antmicro/polarfire-som/assets/previews/layer1.png

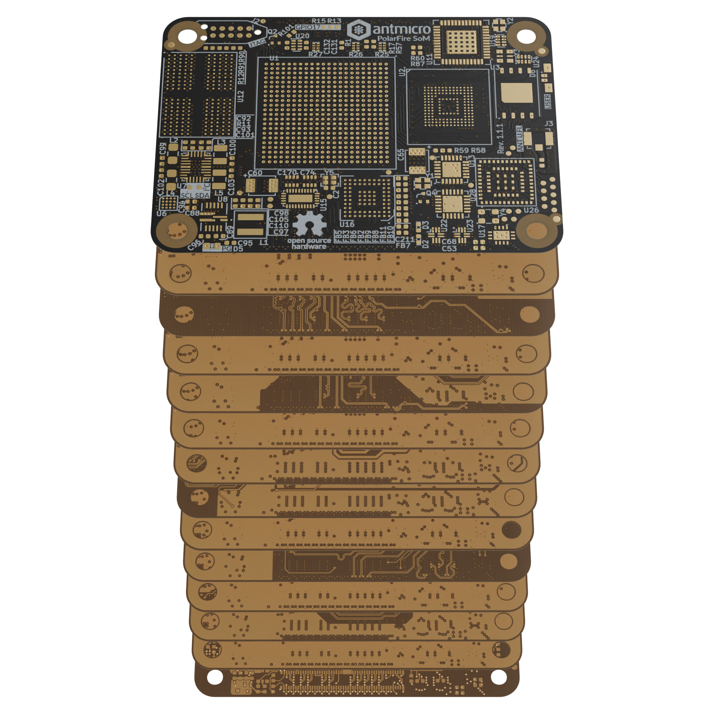
assets/previews/layer1.png
