antmicro/polarfire-som/assets/previews/layer2.png

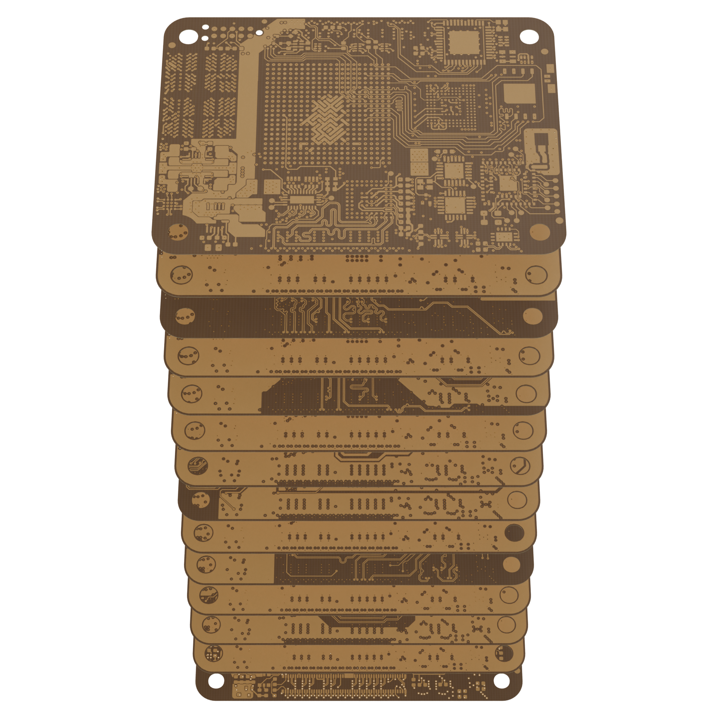
assets/previews/layer2.png
