antmicro/polarfire-som/assets/previews/layer4.png

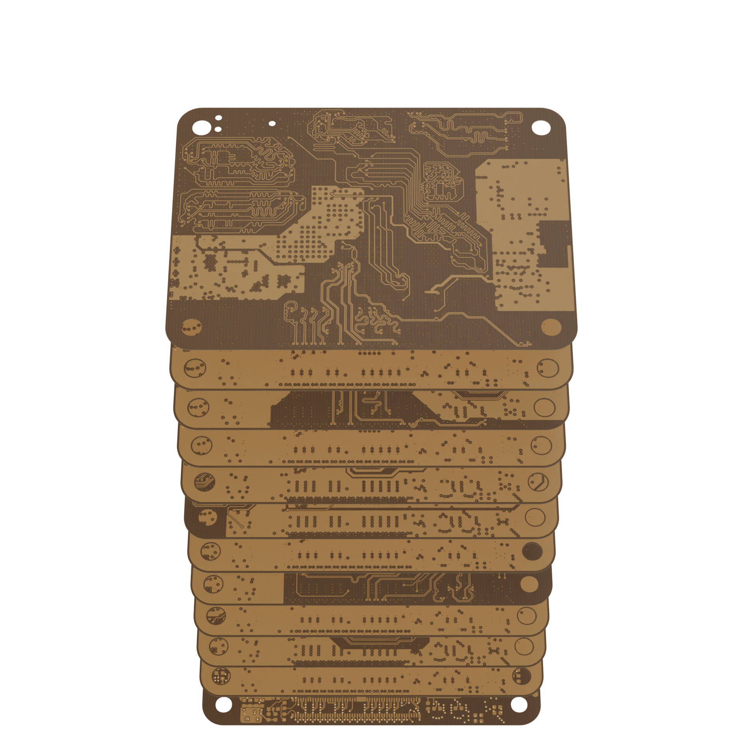
assets/previews/layer4.png
