antmicro/polarfire-som/assets/previews/layer9.png

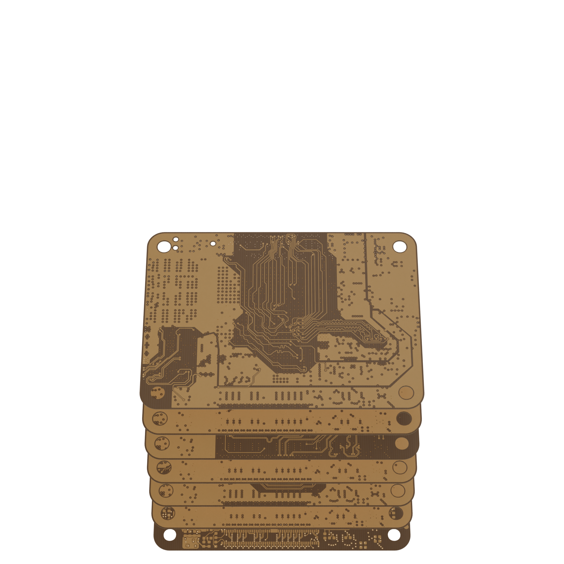
assets/previews/layer9.png
