antmicro/polarfire-som/assets/previews/layer11.png

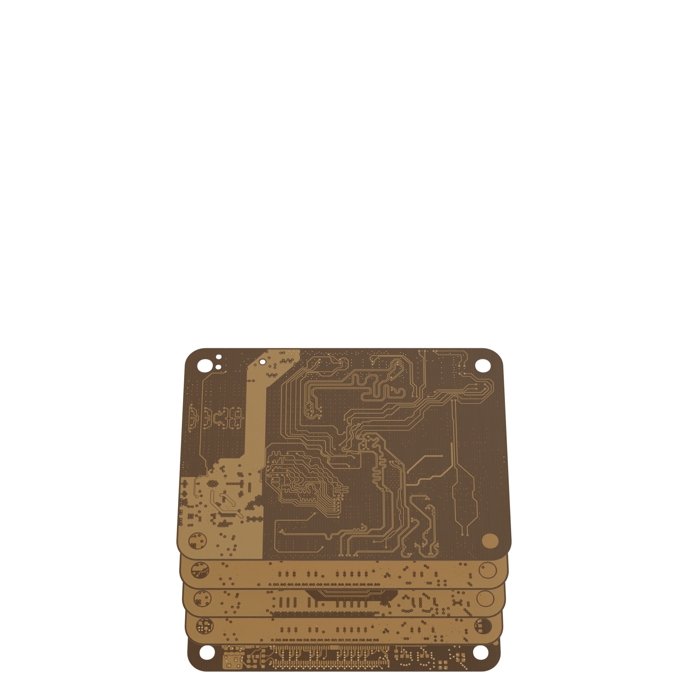
assets/previews/layer11.png
