antmicro/polarfire-som/assets/previews/layer13.png

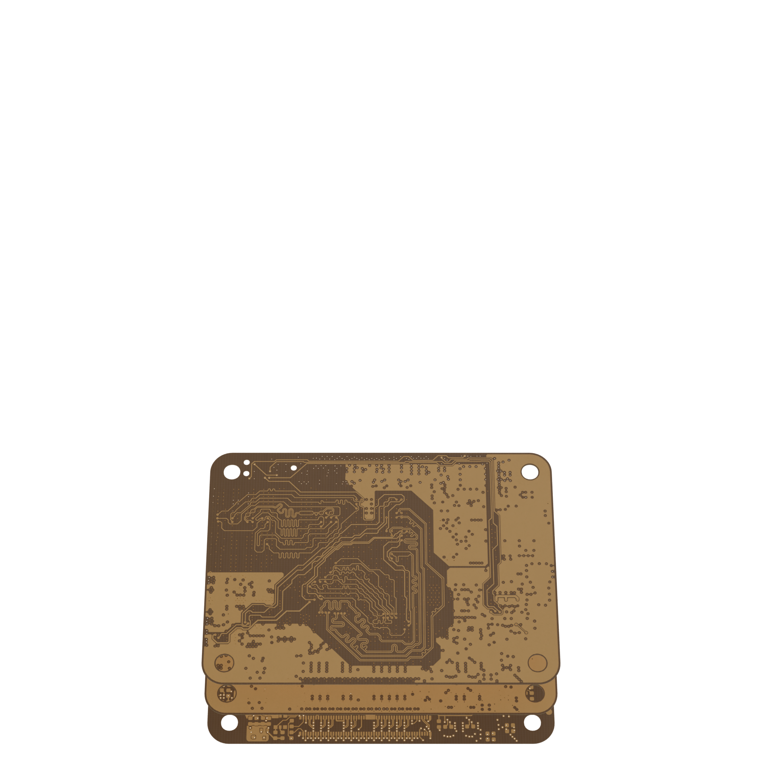
assets/previews/layer13.png
