antmicro/polarfire-som/assets/previews/leftB.png

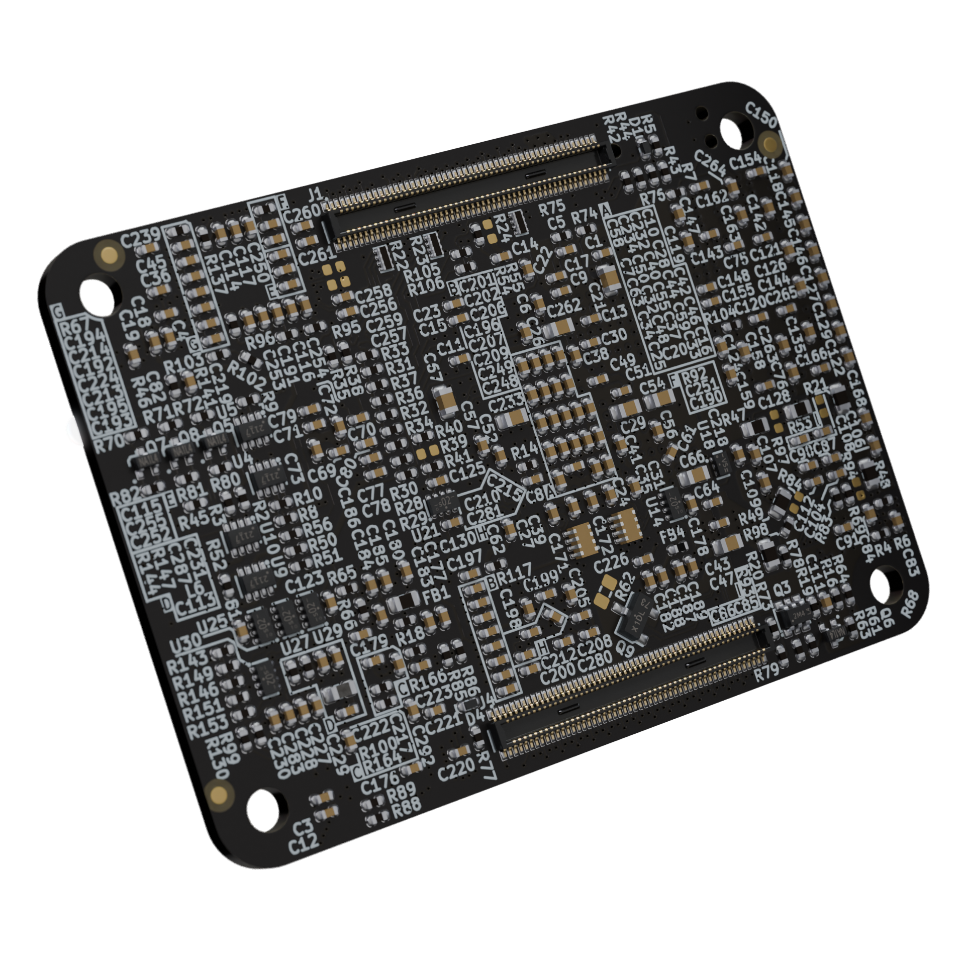
assets/previews/leftB.png
