antmicro/polarfire-som/assets/previews/leftT.png

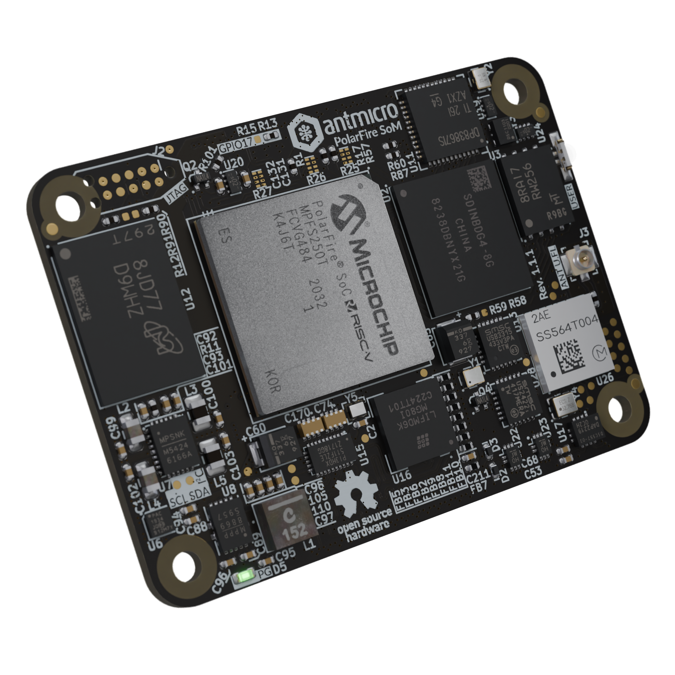
assets/previews/leftT.png
