antmicro/polarfire-som/assets/previews/orthoB.png

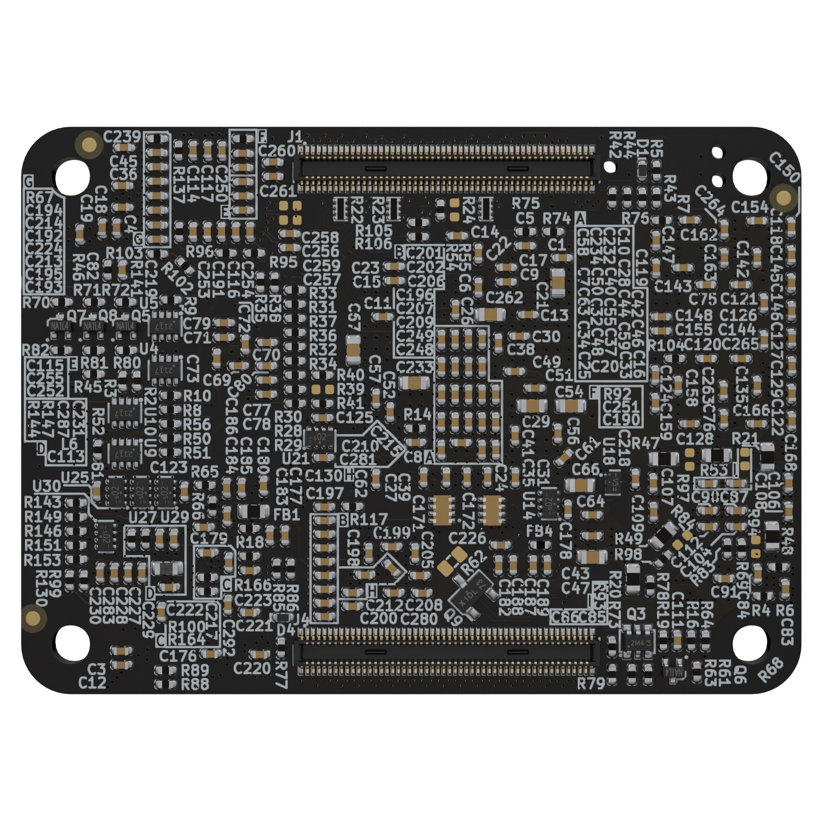
assets/previews/orthoB.png
