antmicro/polarfire-som/assets/previews/orthoT.png

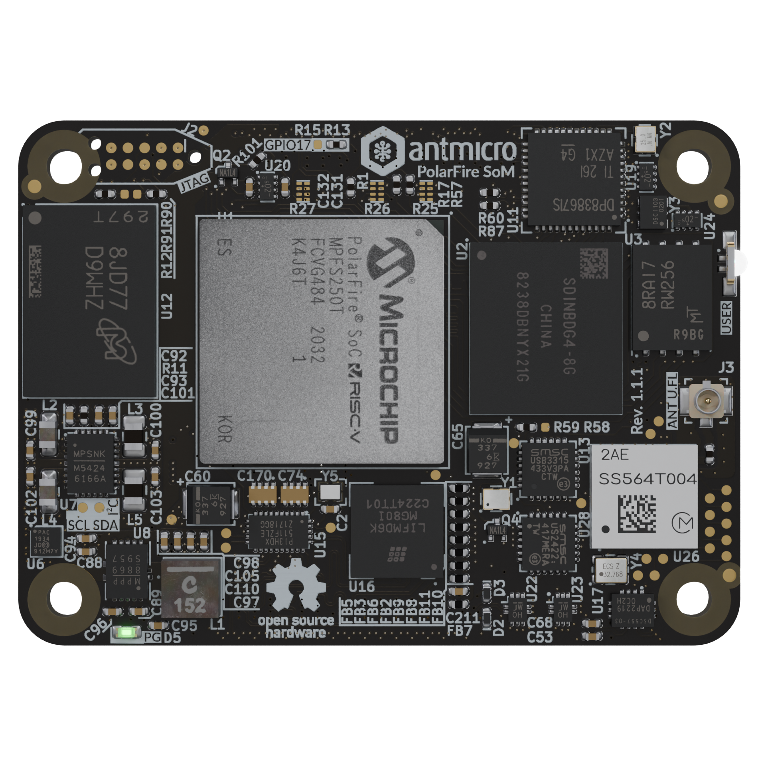
assets/previews/orthoT.png
