antmicro/polarfire-som/assets/previews/rightB.png

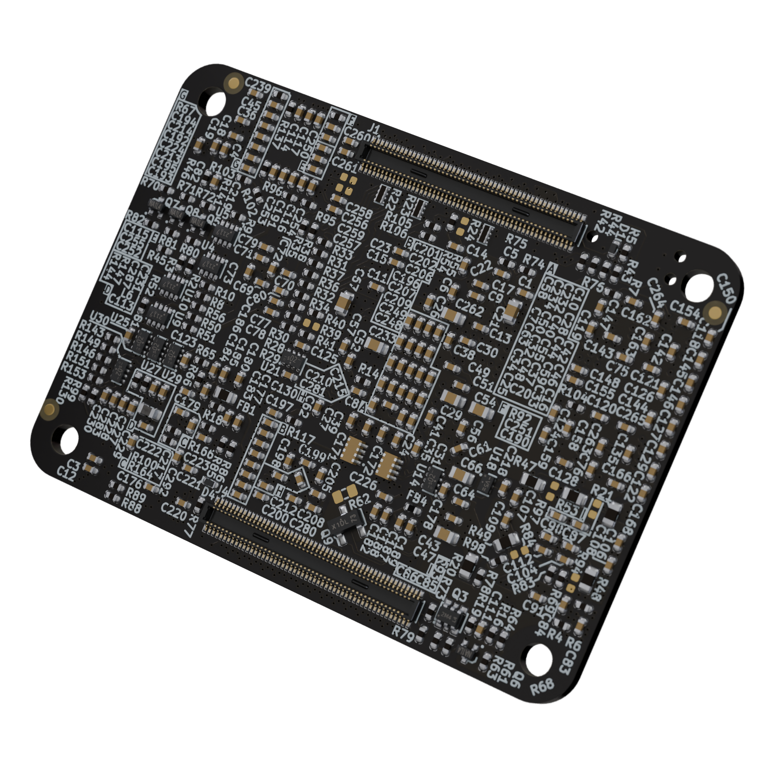
assets/previews/rightB.png
