antmicro/polarfire-som/assets/previews/rightT.png

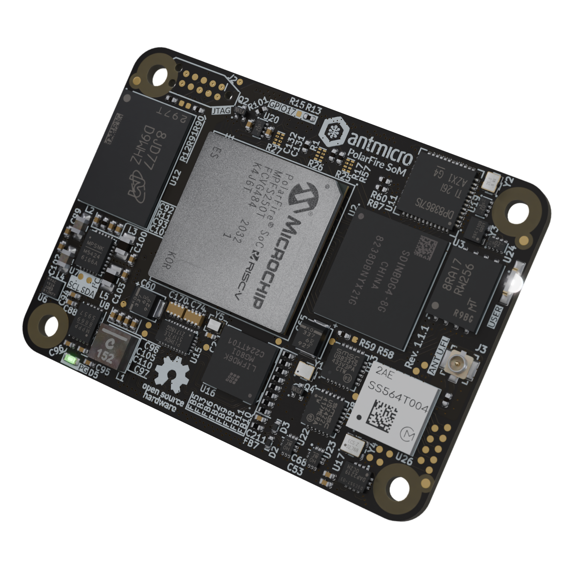
assets/previews/rightT.png
