antmicro/polarfire-som/assets/wireframe/wireframe_wireframe_descriptions_bottom.png

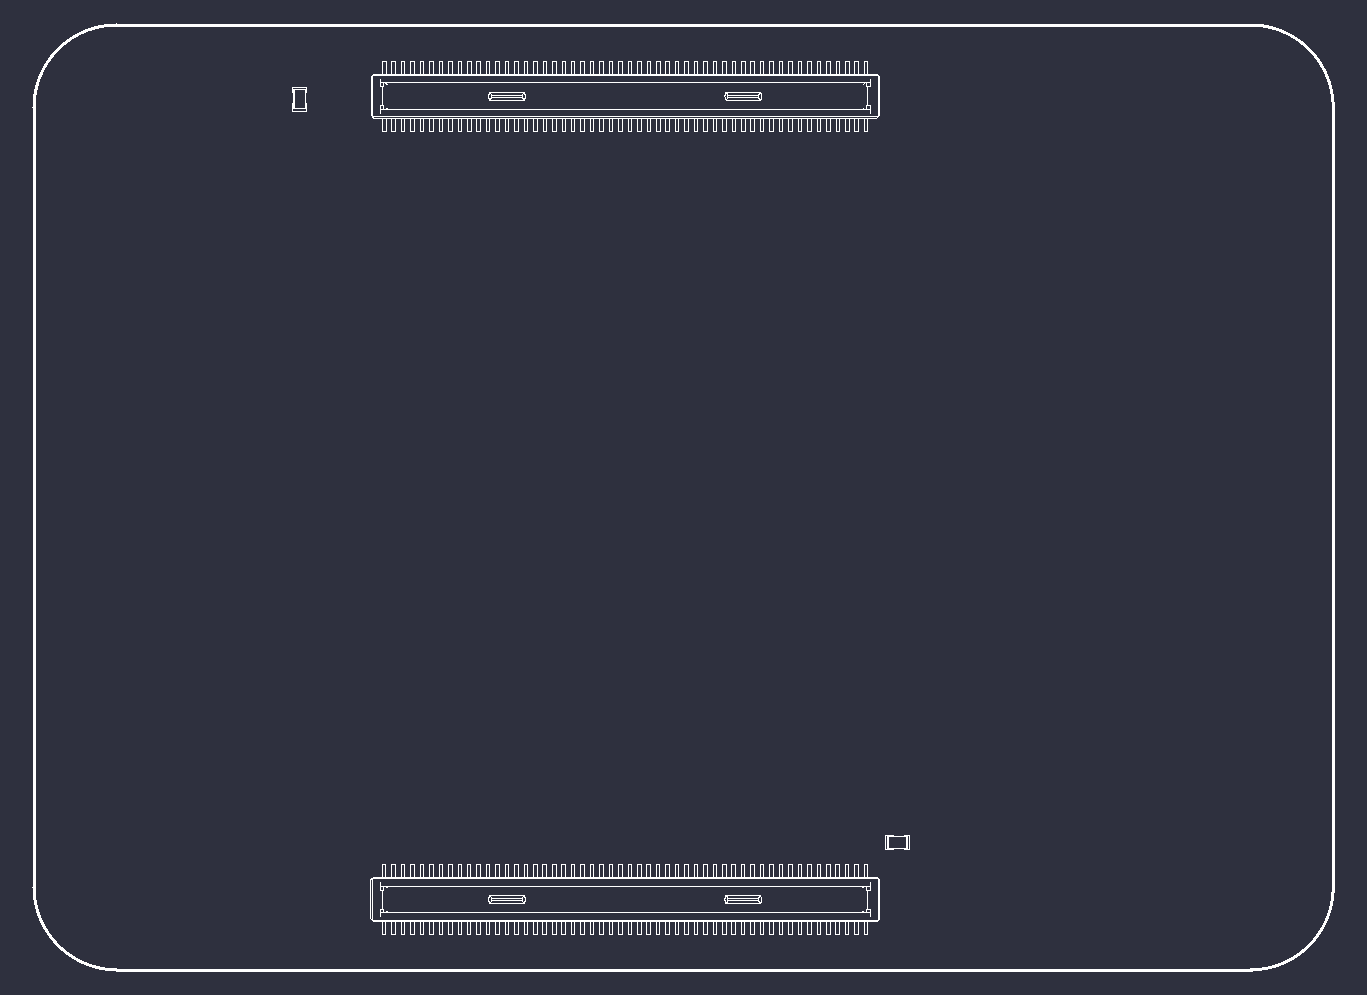
assets/wireframe/wireframe_wireframe_descriptions_bottom.png
