antmicro/polarfire-som/assets/wireframe/wireframe_wireframe_descriptions_top.png

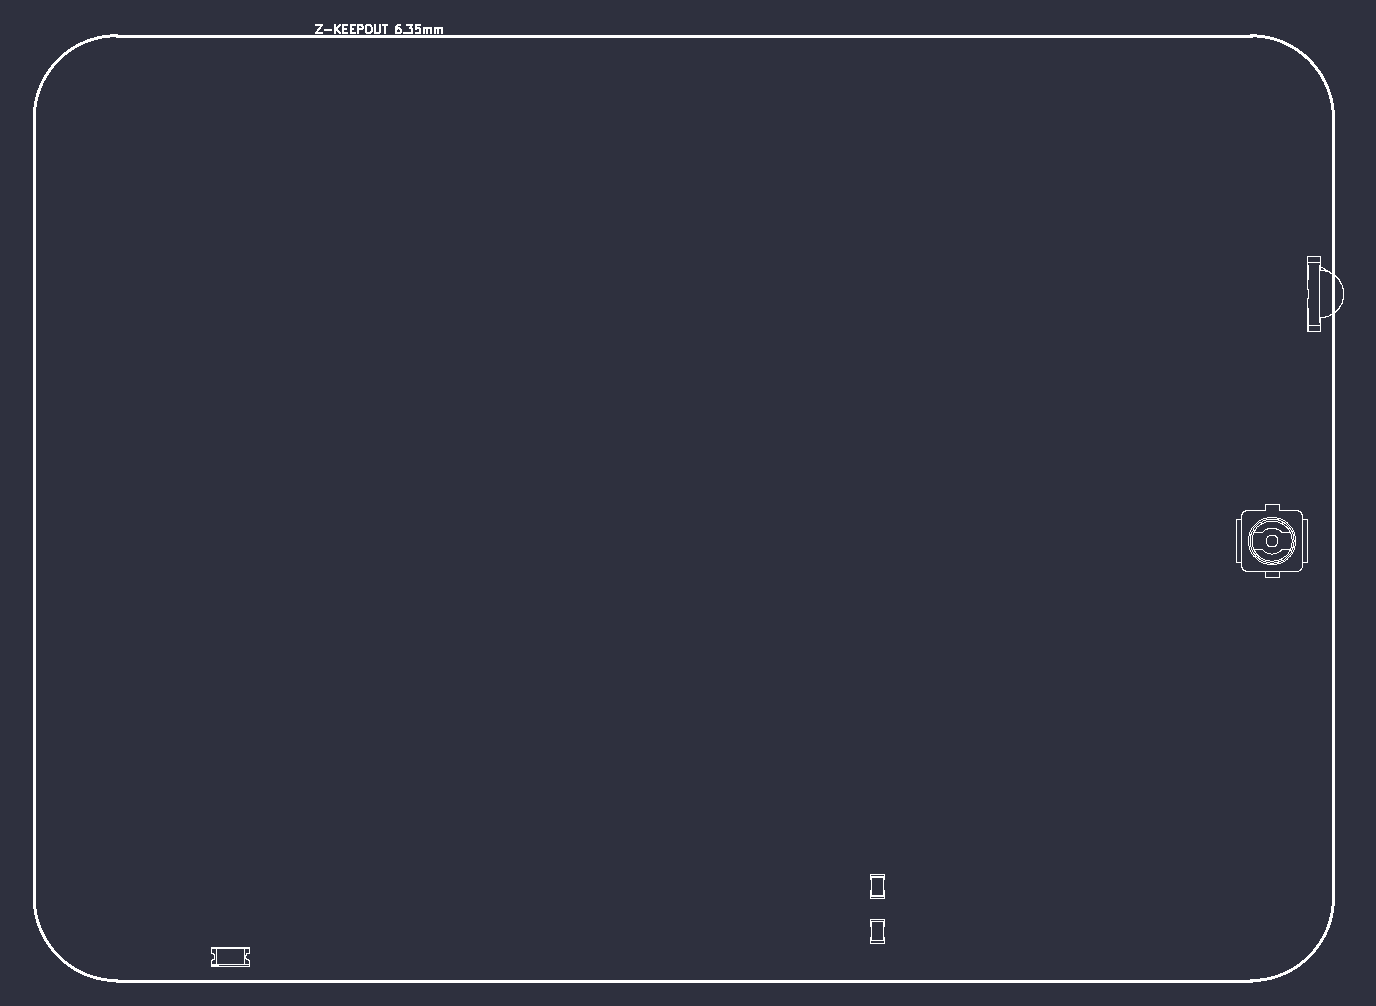
assets/wireframe/wireframe_wireframe_descriptions_top.png
