antmicro/polarfire-som/assets/wireframe/wireframe_wireframe_dimensions.png

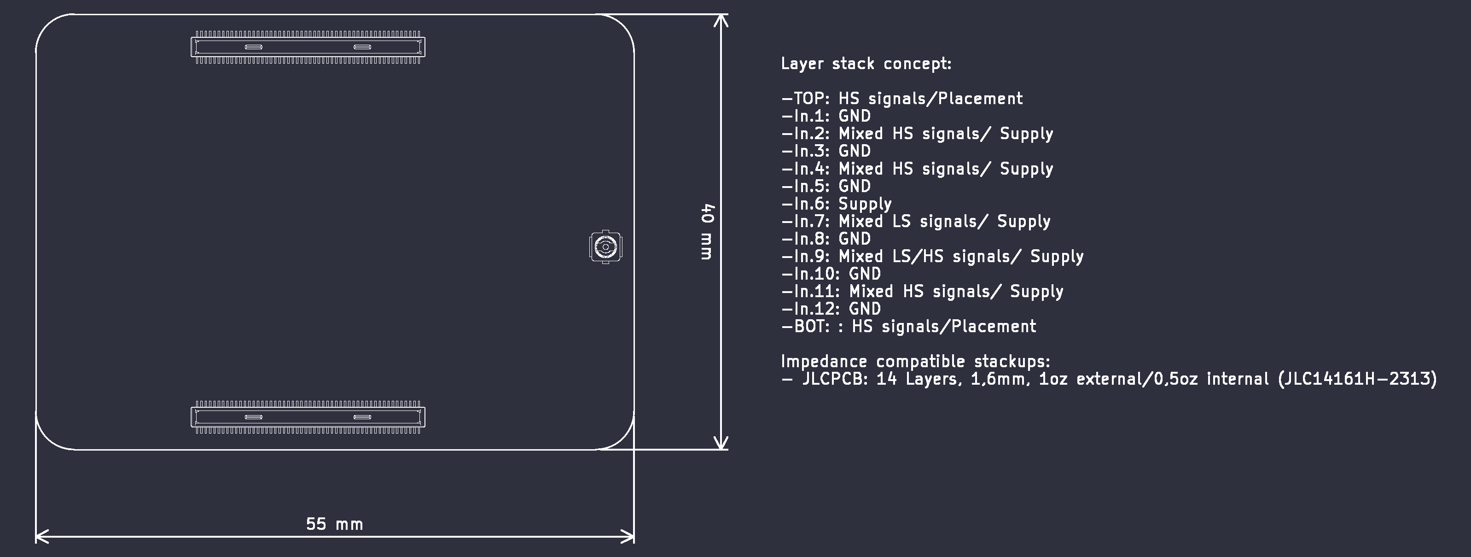
assets/wireframe/wireframe_wireframe_dimensions.png
