antmicro/polarfire-som/assets/wireframe/wireframe_wireframe_dimensions_top.png

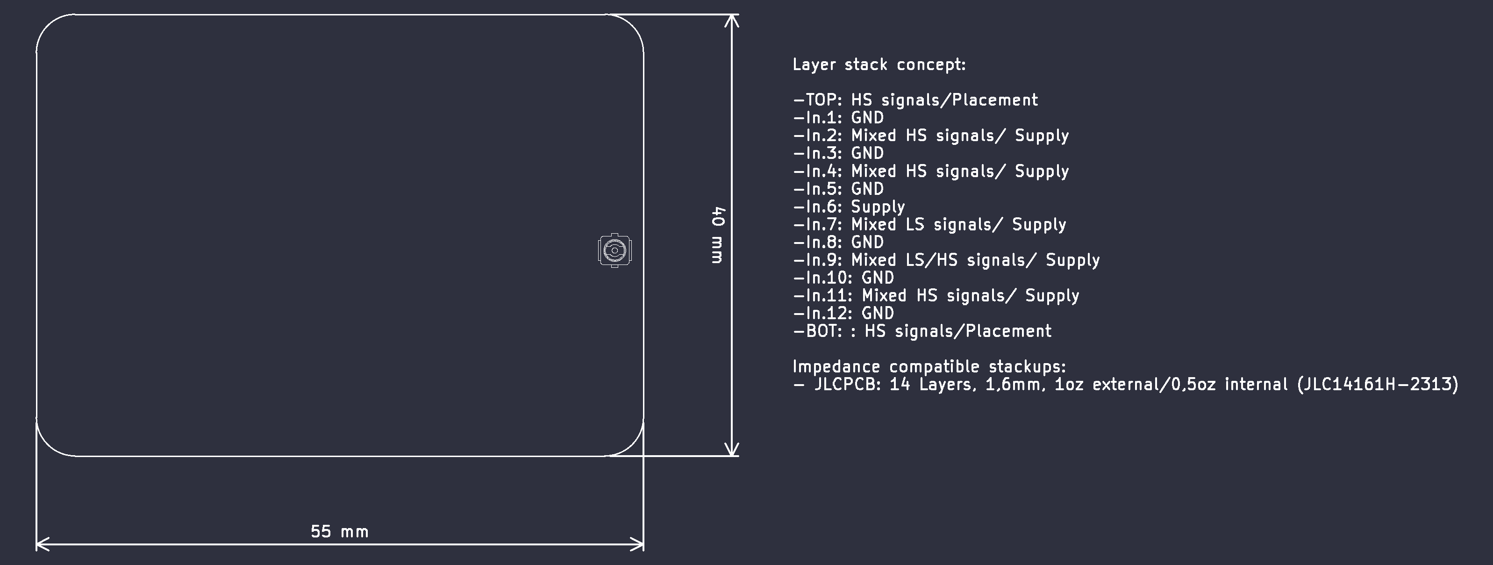
assets/wireframe/wireframe_wireframe_dimensions_top.png
